eb-margolis-neuroscience-lab/Spout/Spout_Construction_Guide/images/3d_print_file_image.png

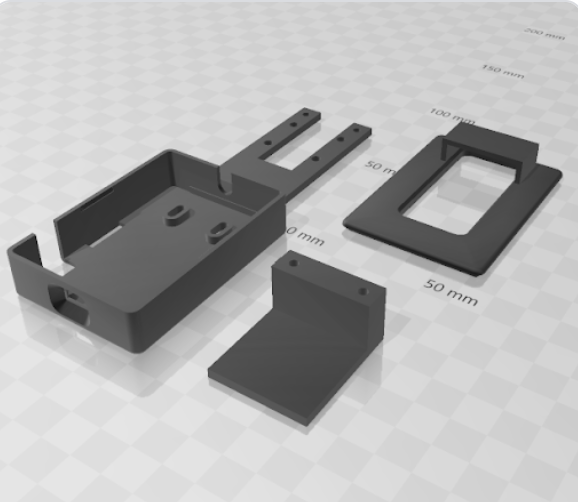
Spout_Construction_Guide/images/3d_print_file_image.png
