eb-margolis-neuroscience-lab/Spout/Spout_Construction_Guide/images/finished_licko.jpg

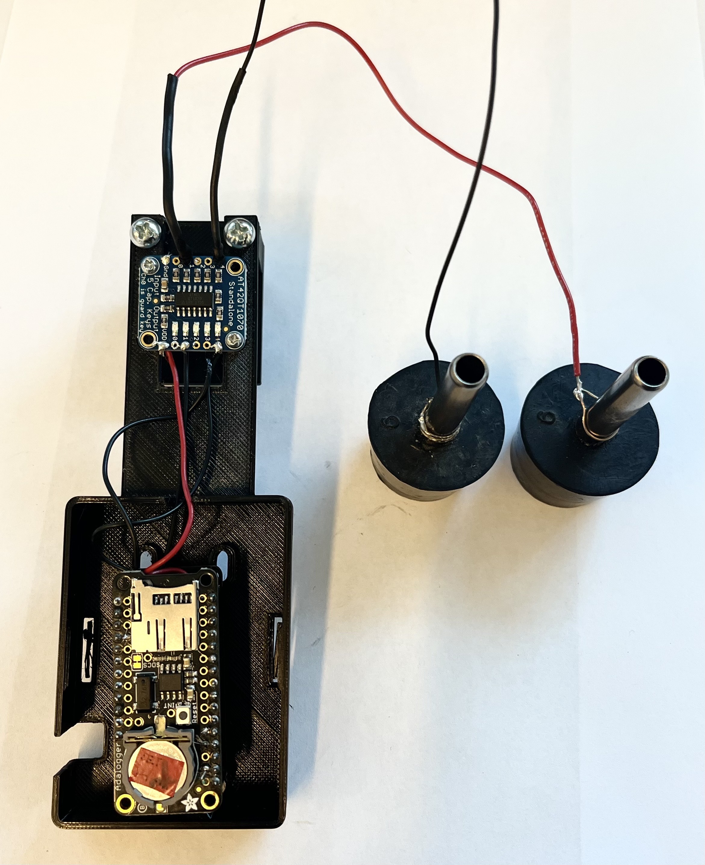
Spout_Construction_Guide/images/finished_licko.jpg
