eb-margolis-neuroscience-lab/Spout/Spout_Construction_Guide/images/licko_ready.png

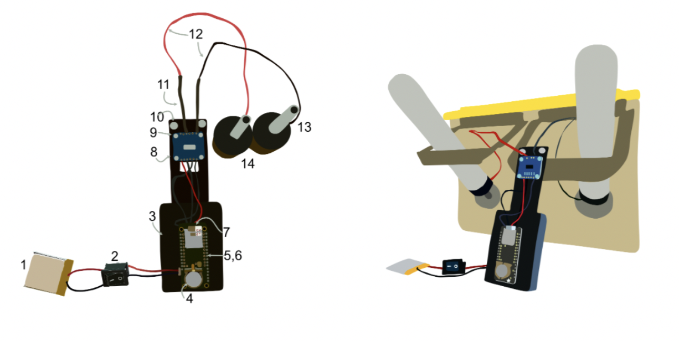
Spout_Construction_Guide/images/licko_ready.png
