eb-margolis-neuroscience-lab/Spout/Spout_Construction_Guide/images/lickometer_illustration_with_cage.png

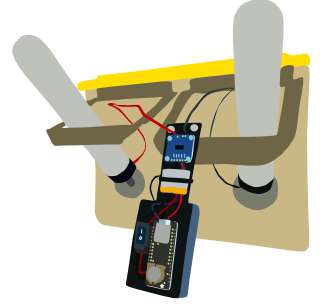
Spout_Construction_Guide/images/lickometer_illustration_with_cage.png
